edge-tech-eu/SmartEVSE/Controllers/Read_DSMR5_SmartMeter/ConnectionDiagram_DSMR5_Pico2W.png

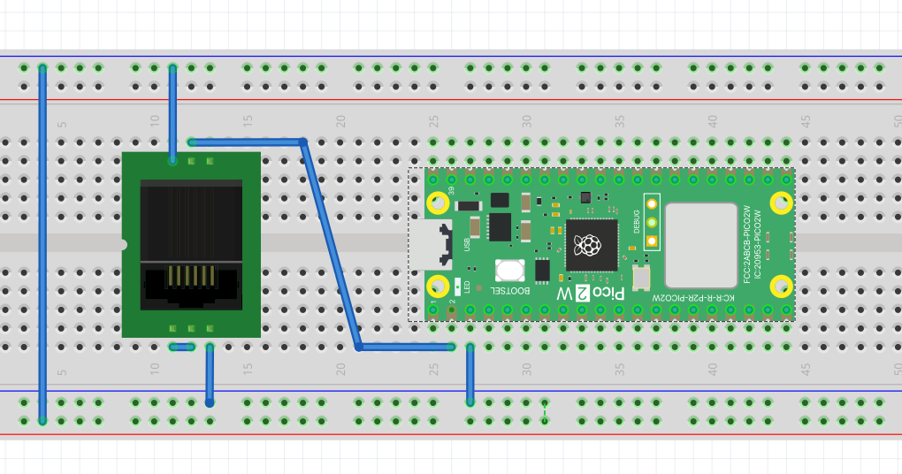
Controllers/Read_DSMR5_SmartMeter/ConnectionDiagram_DSMR5_Pico2W.png
