edge-tech-eu/SmartEVSE/installation/module-site-kl.png

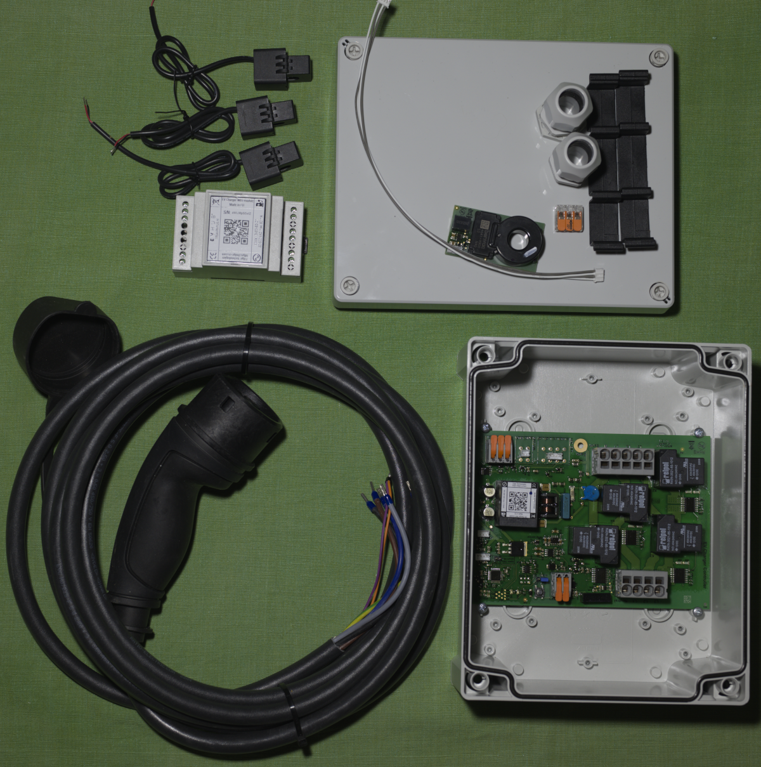
installation/module-site-kl.png
