edge-tech-eu/SmartEVSE/Controllers/Control_Charger/LilyGo_T-Panel-S3_LCD/ev_charging_200x100.c

#ifdef __has_include
    #if __has_include("lvgl.h")
        #ifndef LV_LVGL_H_INCLUDE_SIMPLE
            #define LV_LVGL_H_INCLUDE_SIMPLE
        #endif
    #endif
#endif

#if defined(LV_LVGL_H_INCLUDE_SIMPLE)
    #include "lvgl.h"
#else
    #include "lvgl/lvgl.h"
#endif


#ifndef LV_ATTRIBUTE_MEM_ALIGN
#define LV_ATTRIBUTE_MEM_ALIGN
#endif

#ifndef LV_ATTRIBUTE_IMG_EV_CHARGING_200X100
#define LV_ATTRIBUTE_IMG_EV_CHARGING_200X100
#endif

const LV_ATTRIBUTE_MEM_ALIGN LV_ATTRIBUTE_LARGE_CONST LV_ATTRIBUTE_IMG_EV_CHARGING_200X100 uint8_t ev_charging_200x100_map[] = {
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
