edge-tech-eu/SmartEVSE/Controllers/Control_Charger/M5Stack-CoreS3-SE-IOT_DSMR/SmartEVSE.h

#ifndef SMARTEVSE_h
#define SMARTEVSE_h

typedef struct {
  unsigned long ts;
  bool isNew;
  unsigned char cable_current;
  double c[3];
  double v[3];
  double kwh_session;
  double kwh_total;
  unsigned char state;
  unsigned char error;
  unsigned char temperature;
  unsigned int error_count;
  unsigned int count;
} ChargerState;

void smart_evse_init();
void smart_evse_set_phases(int address, bool isPhases3);
bool smart_evse_is_32_amp(int address);
void smart_evse_get_charger_state(int address, ChargerState *charger_state);
bool smart_evse_get_serial(int address, int *serial);
bool smart_evse_get_fw_version(int address, int *version);
void smart_evse_persist_settings(int address);
void smart_evse_get_max_currents(int address);
void smart_evse_get_state(int address);
void smart_evse_get_temperature(int address);
void smart_evse_get_current_draw(int address);
void smart_evse_get_session_energy(int address);
void smart_evse_get_output_voltage(int address);
void smart_evse_set_max_current(int address, int max_current, int max_current_next_second);
void smart_evse_set_magic(int address, int magic);

#endif
