edge-tech-eu/SmartEVSE/Controllers/Control_Charger/LilyGo_T-Panel-S3_LCD/Board.h

#ifndef BOARD_h
#define BOARD_h

// this is file is included in all general files
// but is specific for:
// 
// LilyGo T-Panel S3 RS485

#include "pin_config.h"

#define DEBUG_PRINTF	Serial.printf

#endif
