edge-tech-eu/SmartEVSE/Controllers/Control_Charger/M5Stack-CoreS3-SE-IOT_DSMR/UI.h

#define UI_h
#include "SmartEVSE.h"
void ui_init();
void ui_delay_untill_tapped(unsigned long delay);
void ui_splash();
void ui_start_update();
void ui_end_update();
void ui_start_up();
void ui_start_up_add_line(char *line);
void ui_start_up_add_line_error(char *line);
void ui_setup_main(int board_max_current, int initial_phases);
void ui_set_advertized(int value);
void ui_set_state(int state);
void ui_set_ev_values(ChargerState charger_state);
void ui_unset_ev_values();
void ui_set_home_values(double home_current[3]);
void ui_unset_home_values();
void ui_process();
void ui_clear();
#define POS_X (16+18)
#define POS_Y 8
#define POS_DX 12
#define POS_DY 16
#define POS_Y_L1 (POS_DY*1.5)
#define POS_Y_L2 (POS_DY*2.5)
#define POS_Y_L3 (POS_DY*3.5)
#define POS_Y_KWH_SESSION (POS_DY*5)
#define POS_Y_KWH_TOTAL (POS_DY*6)
#define POS_X_KWH (7*POS_DX)
#define POS_X_EV_A 4
#define POS_X_EV_V 10
#define POS_X_HOME_A 15
#define STATE_X POS_X
#define STATE_Y 136
#define STATE_V_X (7 * POS_DX)
#define ADVERTIZED_X POS_X
#define ADVERTIZED_Y 160
#define ADVERTIZED_V_X (13 * POS_DX)
#define ADVERTIZED_V_Y 0
#define SLIDER_X 10
#define SLIDER_Y 190
#define SLIDER_WIDTH 300
#define SLIDER_HEIGHT 40
#define BUTTON_X (POS_X+230)
#define BUTTON_Y 156
#define BUTTON_WIDTH 24
#define BUTTON_HEIGHT 24
  #define DEFAULT_FONT        fonts::Font0
  #define DEFAULT_TEXT_COLOR  WHITE
  #define ERROR_TEXT_COLOR    RED
  #define DEFAULT_BG_COLOR    BLACK
  #define SPLASH_COLOR_1    WHITE
  #define SPLASH_COLOR_2    RED
  #define SPLASH_FONT       fonts::FreeMonoBold12pt7b
  #define SPLASH_FONT_DX    14
  #define SPLASH_FONT_DY    12
  #define SPLASH_FONT_SIZE  2
  #define SPLASH_WIDTH      280
  #define SPLASH_HEIGHT     120
  #define SPLASH_ROUNDNESS  (SPLASH_HEIGHT/3)
  #define SPLASH_X          ((320 - SPLASH_WIDTH)/2)
  #define SPLASH_Y          ((240 - SPLASH_HEIGHT)/2)
  #define SPLASH_TEXT_1_DX  15
  #define SPLASH_TEXT_1_DY  38
  #define SPLASH_TEXT_2_DX  (SPLASH_TEXT_1_DX+5*(SPLASH_FONT_DX*SPLASH_FONT_SIZE))
  #define SPLASH_TEXT_2_DY  38
  #define SPLASH_DIAG_DX    40
